obstundgemuese26/BlueNoise26/images/00.jpg

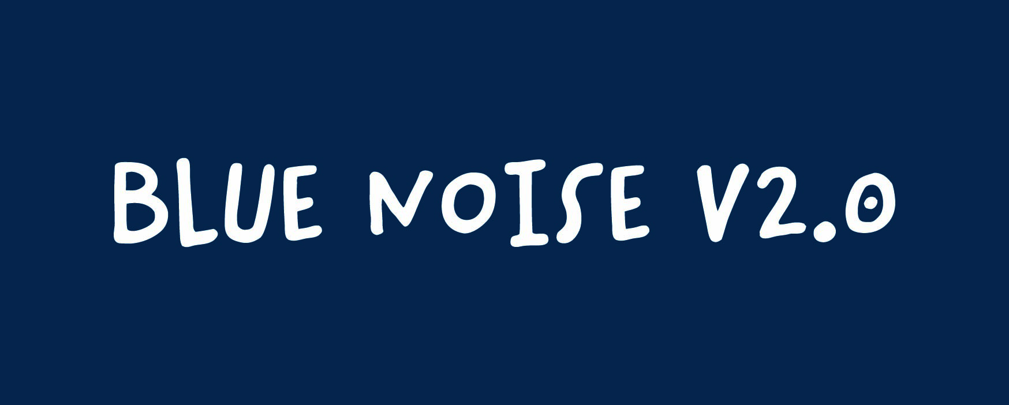
images/00.jpg
