obstundgemuese26/BlueNoise26/images/BlueNoise1.jpg

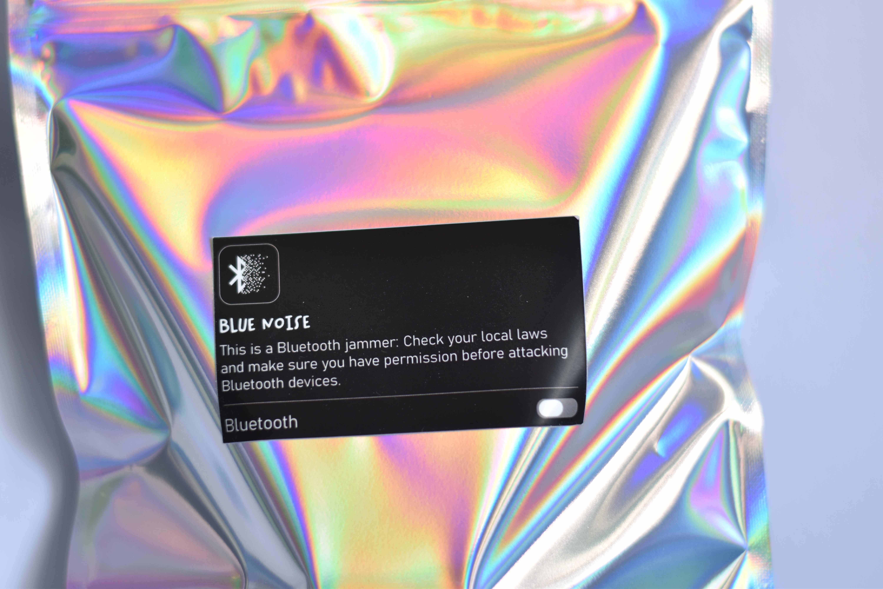
images/BlueNoise1.jpg
