obstundgemuese26/BlueNoise26/images/Connect2.png

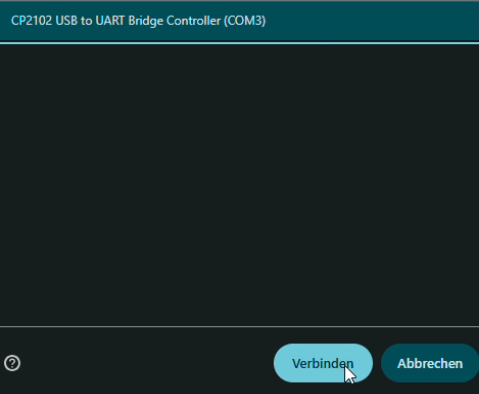
images/Connect2.png
