obstundgemuese26/BlueNoise26/images/upload.png

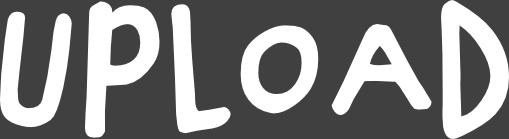
images/upload.png
